hugomorenocamin/bestiasdecarga/RECEIVER/STL/part#1.stl

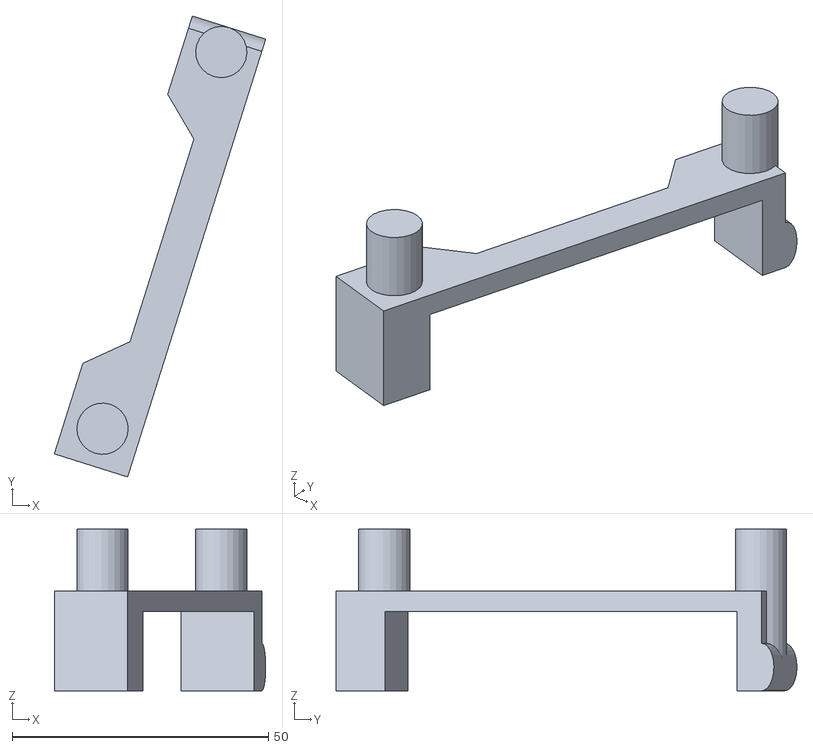
[picture p18: CAD file, 2026-06-07]
RECEIVER/STL/part#1.stl
41.2 x 89.9 x 31.5
