hugomorenocamin/bestiasdecarga/SOLENOID-DRIVEN MALLET/STL/part#2.stl

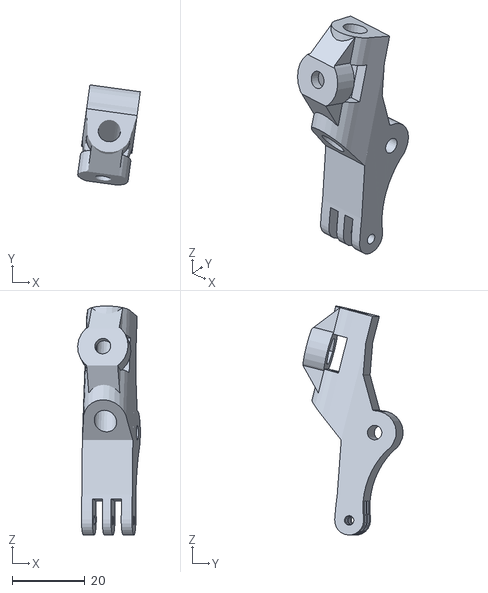
[picture p19: CAD file, 2026-06-07]
SOLENOID-DRIVEN MALLET/STL/part#2.stl
17.3 x 27.6 x 63.0
