hugomorenocamin/bestiasdecarga/RECEIVER/STL/part#4.stl

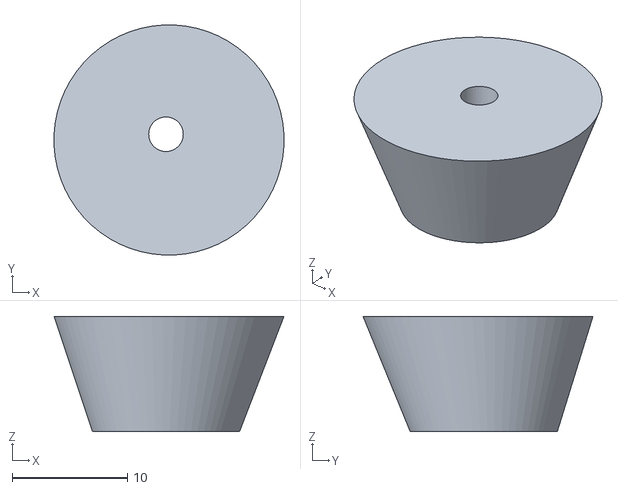
[picture p20: CAD file, 2026-06-07]
RECEIVER/STL/part#4.stl
20.0 x 20.0 x 10.0
