hugomorenocamin/bestiasdecarga/RESPIRATION BELT/Assembly 3d drawing.jpg

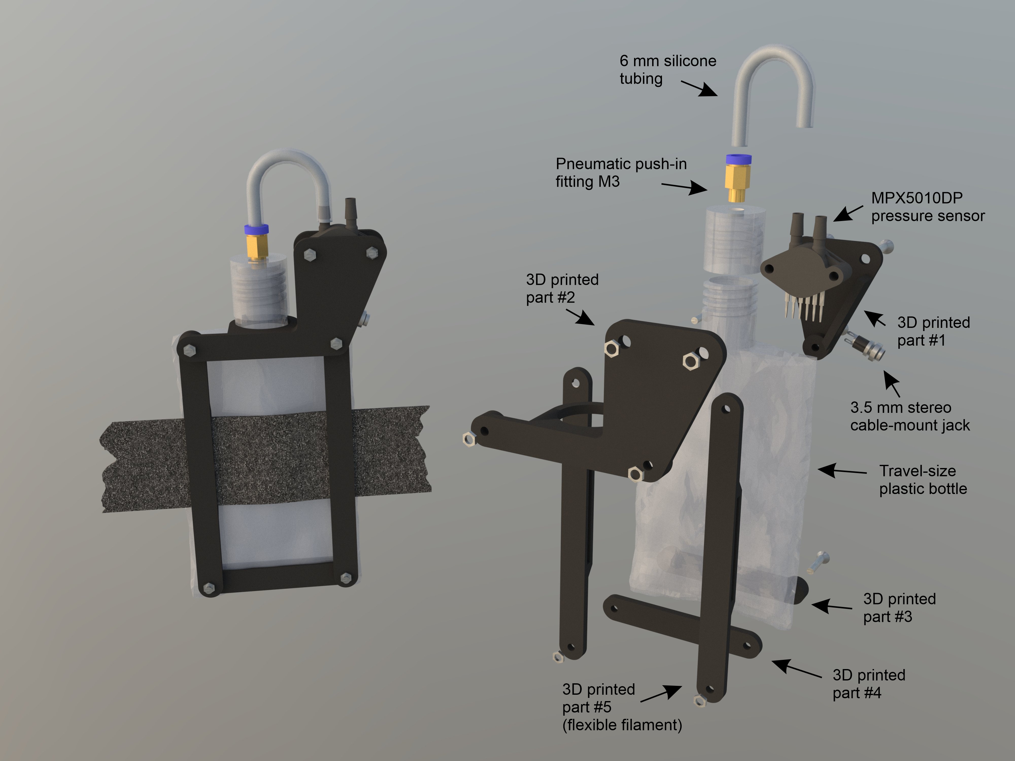
RESPIRATION BELT/Assembly 3d drawing.jpg
